P3Vu/Projekt-grupowy/Software/Czujnik BME280/nucleo.jpg

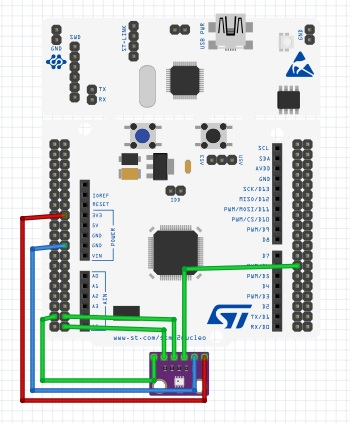
Software/Czujnik BME280/nucleo.jpg
